EricAustinUK/home_power_management/software/src/home_manager/weather_data.rs

use serde::Deserialize;
use thiserror::Error;
use crate::home_manager::ml_engine::WeatherFeatures;

#[derive(Debug, Error)]
pub enum WeatherDataError {
    #[error("Error converting date from weather API data")]
    DateConversion(),

    #[error("Error converting floats from weather API data")]
    FloatConversion(),

    #[error("Weather API returned an unexpected number of records")]
    DataOverflow()
}

#[derive(Clone, Deserialize)]
pub struct WeatherData{
    pub hourly: HourData
}

#[derive(Clone, Deserialize)]
pub struct HourData {
    pub time: [String; 24],
    pub shortwave_radiation: [f32; 24],
    pub direct_radiation: [f32; 24],
    pub diffuse_radiation: [f32; 24],
    pub cloud_cover: [f32; 24],
    pub temperature_2m: [f32; 24]
}

impl TryInto<WeatherFeatures> for WeatherData {
    type Error = WeatherDataError;
    fn try_into(self) -> Result<WeatherFeatures, Self::Error> {
        let feature_arrs = self.hourly;
        
        let mut hour_sin = [0.0; 24];
        let mut hour_cos = [0.0; 24];


        let mut result = WeatherFeatures {
            features: [[0.0; 9]; 24],
        };


        let year:u16 = feature_arrs.time[0].get(0..4)
            .ok_or(WeatherDataError::DateConversion())?
            .parse()
            .map_err(|_| WeatherDataError::DateConversion())?;
        let month:usize = feature_arrs.time[0].get(5..7)
            .ok_or(WeatherDataError::DateConversion())?
            .parse()
            .map_err(|_| WeatherDataError::DateConversion())?;
        let day:u16 = feature_arrs.time[0].get(8..10)
            .ok_or(WeatherDataError::DateConversion())?
            .parse()
            .map_err(|_| WeatherDataError::DateConversion())?;

        let leap = match year {
            y if y % 400 == 0 => true,
            y if y % 100 == 0 => false,
            y if y % 4 == 0 => true,
            _ => false,
        };

        let month_arr:[usize;12] = [31,
            { if leap {29} else {28} },
            31, 30, 31, 30, 31, 31, 30, 31, 30, 31
        ];

        let mut year_day:u16 = day;

        for mo_i in 0..(month-1){
            year_day += month_arr[mo_i] as u16;
        }

        let max_year_day:f32 = if leap {366.} else {365.};

        let angle = 2.0 * std::f32::consts::PI * year_day as f32 / max_year_day as f32;

        let year_day_sin = angle.sin();
        let year_day_cos = angle.cos();


        for i in 0..24 {
            let time = &feature_arrs.time[i];
            let hour_str = time
                .get(11..13)
                .ok_or(WeatherDataError::DateConversion())?;

            let hour: f32 = hour_str
                .parse()
                .map_err(|_| WeatherDataError::DateConversion())?;

            let angle = 2.0 * std::f32::consts::PI * hour / 24.0;

            hour_sin[i] = angle.sin();
            hour_cos[i] = angle.cos();

            result.features[i] = [
                year_day_sin as f64,
                year_day_cos as f64,
                hour_sin[i] as f64,
                hour_cos[i] as f64,
                feature_arrs.shortwave_radiation[i] as f64,
                feature_arrs.direct_radiation[i] as f64,
                feature_arrs.diffuse_radiation[i] as f64,
                feature_arrs.cloud_cover[i] as f64,
                feature_arrs.temperature_2m[i] as f64,
            ];
        }

        Ok(result)
    }
}
